agweimar/hackTM/micropython/skeleton/config_sensorboard.py

import time
import machine
import ubinascii 

from controller_sensorboard import Controller


SOFT_SPI = True
IS_ESP32 = True
IS_MICROPYTHON = True

# millisecond
millisecond = time.ticks_ms

# Node Name
UUID = ubinascii.hexlify(machine.unique_id()).decode()  
NODE_NAME = 'SensorBoard_' + UUID
